MAATHES-THILAK-K/METAL_AIR_BMS/IMAGES/WhatsApp Image 2026-07-26 at 10.38.59.jpeg

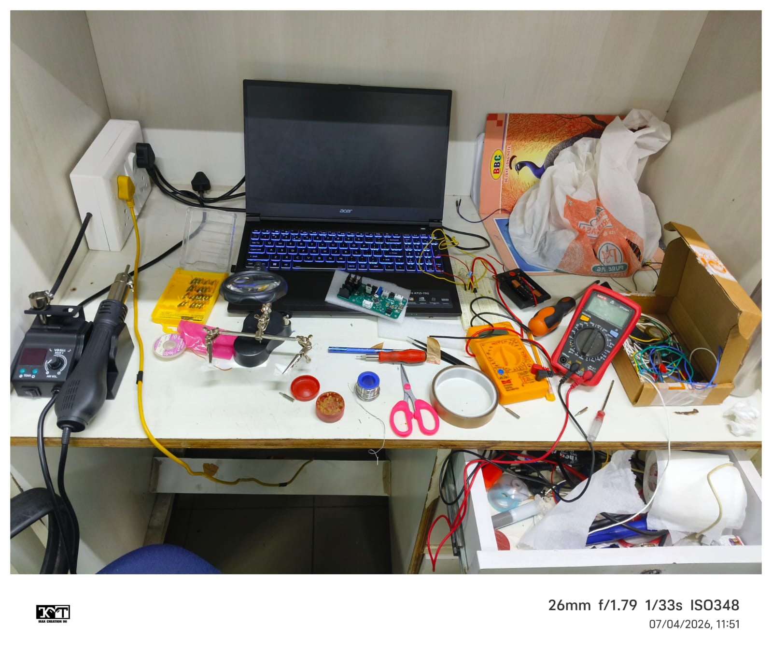
IMAGES/WhatsApp Image 2026-07-26 at 10.38.59.jpeg
